kskelm/parametric-cookie-cutter/radioactive.stl

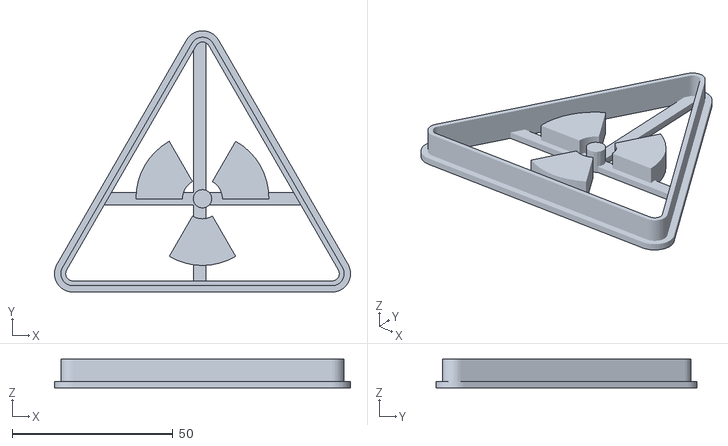
[picture p15: CAD file, 2016-02-29]
radioactive.stl
92.0 x 81.3 x 9.00
