kskelm/parametric-cookie-cutter/radioactive_cut.dxf

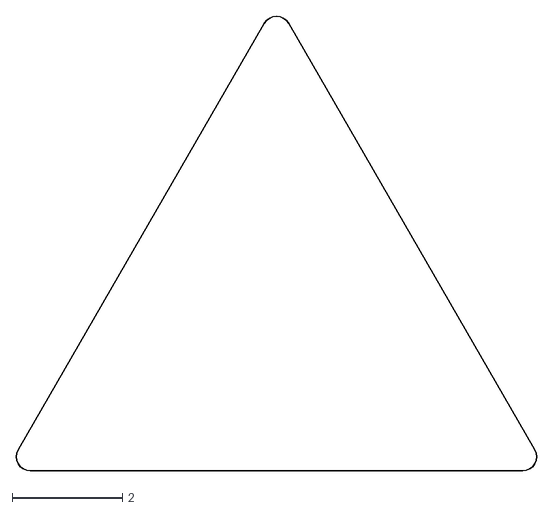
[picture p16: CAD file, 2016-02-25]
radioactive_cut.dxf
9.46 x 8.26
