kskelm/parametric-cookie-cutter/radioactive_imprint.dxf

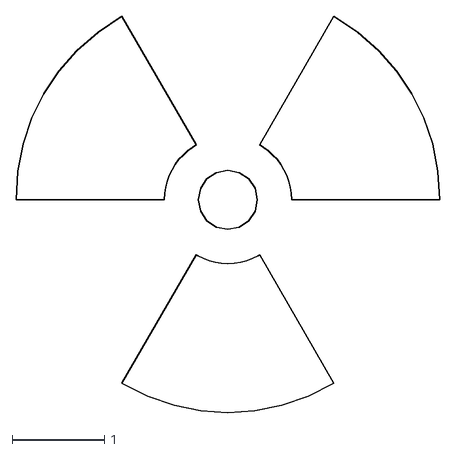
[picture p17: CAD file, 2016-02-25]
radioactive_imprint.dxf
4.59 x 4.29
