kskelm/parametric-cookie-cutter/smiley_face_cut.dxf

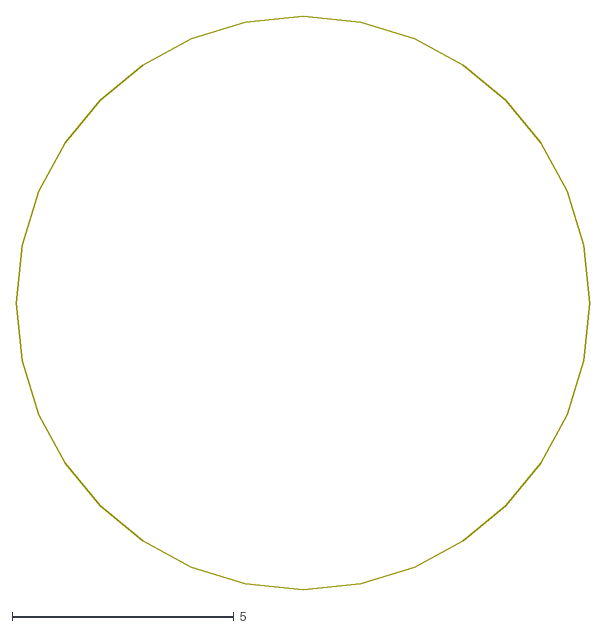
[picture p18: CAD file, 2016-02-25]
smiley_face_cut.dxf
12.9 x 12.9
