kskelm/parametric-cookie-cutter/smiley_face_imprint.dxf

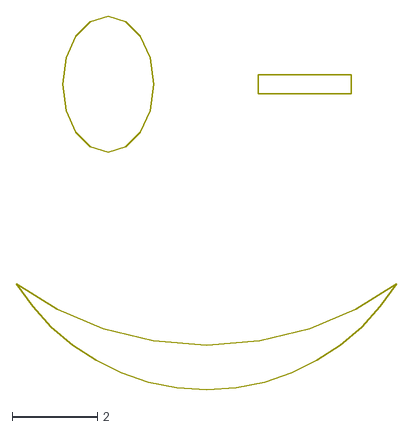
[picture p19: CAD file, 2016-02-25]
smiley_face_imprint.dxf
8.91 x 8.74
